adm1nsys/Micro-Matter-Switch/custom_connect.h

#pragma once

void UserEventsConnect() {
 // Custom action Calling every 200ms while device in pairing mode (no arguments in call)
}

void UserEventsDecommissioning() {
// Decommissioning…
}

void UserEventsBootClick() {
// UserEventsBootClick
}
